GeraKuznetsov/M68K-MBC/Code/Boot/driver/SPI.c

#include "SPI.h"
#include "sys.h"

uint8_t const R1_READY_STATE = 0X00;
/** status for card in the idle state */
uint8_t const R1_IDLE_STATE = 0X01;
/** status bit for illegal command */
uint8_t const R1_ILLEGAL_COMMAND = 0X04;
/** start data token for read or write single block*/
uint8_t const DATA_START_BLOCK = 0XFE;
/** stop token for write multiple blocks*/
uint8_t const STOP_TRAN_TOKEN = 0XFD;
/** start data token for write multiple blocks*/
uint8_t const WRITE_MULTIPLE_TOKEN = 0XFC;
/** mask for data response tokens after a write block operation */
uint8_t const DATA_RES_MASK = 0X1F;
/** write data accepted token */
uint8_t const DATA_RES_ACCEPTED = 0X05;

/** Standard capacity V1 SD card */
uint8_t const SD_CARD_TYPE_SD1 = 1;
/** Standard capacity V2 SD card */
uint8_t const SD_CARD_TYPE_SD2 = 2;
/** High Capacity SD card */
uint8_t const SD_CARD_TYPE_SDHC = 3;

#define CS_LOW() SYS_PORT_RESET(SYS_OUT_PORT_SPI_CE0)
#define CS_HIGH() SYS_PORT_SET(SYS_OUT_PORT_SPI_CE0)

static volatile DSTATUS Stat = STA_NOINIT;	/* Disk status */
u8 CardType;

DSTATUS mmc_disk_status (void)
{
	return Stat;
}

static int wait_ready (	/* 1:Ready, 0:Timeout */
	u16 wt			/* Timeout [ms] */
){
	u8 d;

	wt /= 10;
	for(u32 i = 0; d != 0xFF & i < 125000; i++){ //TODO: timer
		d = SPI_SEND(0xFF);
	}

	return (d == 0xFF) ? 1 : 0;
}

static void deselect(){
	CS_HIGH();		/* Set CS# high */
	SPI_SEND(0xFF);	/* Dummy clock (force DO hi-z for multiple slave SPI) */
}

static int select()	/* 1:Successful, 0:Timeout */
{
	CS_LOW();		/* Set CS# low */
	SPI_SEND(0xFF);	/* Dummy clock (force DO enabled) */

	if (wait_ready(500)) return 1;	/* Leading busy check: Wait for card ready */

	deselect();		/* Timeout */
	return 0;
}

u8 send_cmd (		/* Returns R1 resp (bit7==1:Send failed) */
	u8 cmd,		/* Command index */
	u32 arg		/* Argument */
)
{
	u8 n, res;


	if (cmd & 0x80) {	/* ACMD<n> is the command sequense of CMD55-CMD<n> */
		cmd &= 0x7F;
		res = send_cmd(CMD55, 0);
		if (res > 1) return res;
	}

	/* Select the card and wait for ready except to stop multiple block read */
	if (cmd != CMD12) {
		deselect();
		if (!select()) return 0xFF;
	}

	/* Send command packet */
	SPI_SEND(0x40 | cmd);				/* Start + Command index */
	SPI_SEND((u8)(arg >> 24));		/* Argument[31..24] */
	SPI_SEND((u8)(arg >> 16));		/* Argument[23..16] */
	SPI_SEND((u8)(arg >> 8));			/* Argument[15..8] */
	SPI_SEND((u8)arg);				/* Argument[7..0] */
	n = 0x01;							/* Dummy CRC + Stop */
	if (cmd == CMD0) n = 0x95;			/* Valid CRC for CMD0(0) + Stop */
	if (cmd == CMD8) n = 0x87;			/* Valid CRC for CMD8(0x1AA) Stop */
	SPI_SEND(n);

	/* Receive command response */
	if (cmd == CMD12) SPI_SEND(0xFF);		/* Skip a stuff u8 when stop reading */
	n = 10;								/* Wait for a valid response in timeout of 10 attempts */
	do
		res = SPI_SEND(0xFF);
	while ((res & 0x80) && --n);

	return res;			/* Return with the response value */
}

void panic(unsigned char* message);

DSTATUS mmc_disk_initialize (void)
{
	BYTE n, cmd, ty, ocr[4];
	Stat = STA_NOINIT;

	//power_off();						/* Turn off the socket power to reset the card */
	for(u32 i = 0; i < 125000; i++){	/* Wait for 100ms */
		__asm__("nop ");
	}	

	//if (Stat & STA_NODISK) return Stat;	/* No card in the socket? */

	//power_on();							/* Turn on the socket power */
	SPI_SET_SPEED(SPI_SLOW);
	for (n = 10; n; n--) SPI_SEND(0xFF);	/* 80 dummy clocks */

	ty = 0;
	if (send_cmd(CMD0, 0) == 1) {			/* Put the card SPI mode */
		u16 attempt = 1000;						/* Initialization timeout of 1000 msec */
		if (send_cmd(CMD8, 0x1AA) == 1) {	/* Is the card SDv2? */
			for (n = 0; n < 4; n++) ocr[n] = SPI_SEND(0xFF);	/* Get trailing return value of R7 resp */
			if (ocr[2] == 0x01 && ocr[3] == 0xAA) {				/* The card can work at vdd range of 2.7-3.6V */
				while (attempt && send_cmd(ACMD41, 1UL << 30)){ attempt--;	}/* Wait for leaving idle state (ACMD41 with HCS bit) */
				if (attempt && send_cmd(CMD58, 0) == 0) {		/* Check CCS bit in the OCR */
					for (n = 0; n < 4; n++) ocr[n] = SPI_SEND(0xFF);
					ty = (ocr[0] & 0x40) ? CT_SDC2 | CT_BLOCK : CT_SDC2;	/* Check if the card is SDv2 */
				}
			}
		} else {							/* SDv1 or MMCv3 */
			if (send_cmd(ACMD41, 0) <= 1) 	{
				ty = CT_SDC1; cmd = ACMD41;	/* SDv1 */
			} else {
				ty = CT_MMC3; cmd = CMD1;	/* MMCv3 */
			}
			while (attempt && send_cmd(cmd, 0)){attempt--;};			/* Wait for leaving idle state */
			if (!attempt || send_cmd(CMD16, 512) != 0)	/* Set R/W block length to 512 */
				ty = 0;
		}
	}
	CardType = ty;
	deselect();

	if (ty) {			/* Initialization succeded */
		Stat &= ~STA_NOINIT;		/* Clear STA_NOINIT */
		SPI_SET_SPEED(SPI_FAST);
	} else {			/* Initialization failed */
		//power_off();
	}
	
	//return ty;
	return Stat;
}


void rcvr_spi_multi (
	BYTE *buff,	/* Pointer to read buffer */
	UINT bc		/* Number of bytes to receive */
){
	do {
		*buff = SPI_SEND(0xFF);			/* Store a received byte */
		buff++;
	} while (--bc);
}

static int rcvr_datablock (
	BYTE *buff,			/* Data buffer to store received data */
	UINT btr			/* Byte count (must be multiple of 4) */
){
	BYTE token;

	//Timer1 = 20;
	u32 attempt = 200000;
	do {							/* Wait for data packet in timeout of 200ms */
		token = SPI_SEND(0xFF);
		attempt--;
	} while ((token == 0xFF) && attempt);
	//} while ((token == 0xFF) && Timer1);
	if (token != 0xFE) return 0;	/* If not valid data token, retutn with error */

	rcvr_spi_multi(buff, btr);		/* Receive the data block into buffer */
	SPI_SEND(0xFF);					/* Discard CRC */
	SPI_SEND(0xFF);

	return 1;						/* Return with success */
}

/*-----------------------------------------------------------------------*/
/* Read Sector(s)                                                        */
/*-----------------------------------------------------------------------*/

DRESULT mmc_disk_read (
	BYTE *buff,			/* Pointer to the data buffer to store read data */
	LBA_t sector,		/* Start sector number (LBA) */
	UINT count			/* Sector count (1..128) */
)
{
	BYTE cmd;
	DWORD sect = (DWORD)sector;

	if (!count) return RES_PARERR;
	if (Stat & STA_NOINIT) return RES_NOTRDY;

	if (!(CardType & CT_BLOCK)) sect *= 512;	/* Convert to byte address if needed */

	cmd = count > 1 ? CMD18 : CMD17;			/*  READ_MULTIPLE_BLOCK : READ_SINGLE_BLOCK */
	if (send_cmd(cmd, sect) == 0) {
		do {
			if (!rcvr_datablock(buff, 512)) break;
			buff += 512;
		} while (--count);
		if (cmd == CMD18) send_cmd(CMD12, 0);	/* STOP_TRANSMISSION */
	}
	deselect();

	return count ? RES_ERROR : RES_OK;
}

/*-----------------------------------------------------------------------*/
/* Miscellaneous Functions                                               */
/*-----------------------------------------------------------------------*/

static void xmit_spi_multi (
	const BYTE *p,	/* Data block to be sent */
	UINT cnt		/* Size of data block */
)
{
	do {
		SPI_SEND(*p++);
	} while (--cnt);
}

static int xmit_datablock (
	const BYTE *buff,	/* 512 byte data block to be transmitted */
	BYTE token			/* Data/Stop token */
)
{
	BYTE resp;

	if (!wait_ready(500)) return 0;		/* Leading busy check: Wait for card ready to accept data block */

	SPI_SEND(token);					/* Xmit data token */
	if (token == 0xFD) return 1;		/* Do not send data if token is StopTran */

	xmit_spi_multi(buff, 512);			/* Data */
	SPI_SEND(0xFF); SPI_SEND(0xFF);		/* Dummy CRC */

	resp = SPI_SEND(0xFF);				/* Receive data resp */

	return (resp & 0x1F) == 0x05 ? 1 : 0;	/* Data was accepted or not */

	/* Busy check is done at next transmission */
}

DRESULT mmc_disk_ioctl (
	BYTE cmd,		/* Control code */
	void *buff		/* Buffer to send/receive control data */
)
{
	DRESULT res;
	BYTE n, csd[16], *ptr = buff;
	DWORD csize;
#if FF_USE_TRIM
	LBA_t *range;
	DWORD st, ed;
#endif
#if _USE_ISDIO
	SDIO_CTRL *sdi;
	BYTE rc, *bp;
	UINT dc;
#endif

	if (Stat & STA_NOINIT) return RES_NOTRDY;

	res = RES_ERROR;
	switch (cmd) {
	case CTRL_SYNC :		/* Make sure that no pending write process. Do not remove this or written sector might not left updated. */
		if (select()) res = RES_OK;
		deselect();
		break;

	case GET_SECTOR_COUNT :	/* Get number of sectors on the disk (DWORD) */
		if ((send_cmd(CMD9, 0) == 0) && rcvr_datablock(csd, 16)) {
			if ((csd[0] >> 6) == 1) {	/* SDC ver 2.00 */
				csize = csd[9] + ((WORD)csd[8] << 8) + ((DWORD)(csd[7] & 63) << 16) + 1;
				*(LBA_t*)buff = csize << 10;
			} else {					/* SDC ver 1.XX or MMC*/
				n = (csd[5] & 15) + ((csd[10] & 128) >> 7) + ((csd[9] & 3) << 1) + 2;
				csize = (csd[8] >> 6) + ((WORD)csd[7] << 2) + ((WORD)(csd[6] & 3) << 10) + 1;
				*(LBA_t*)buff = csize << (n - 9);
			}
			res = RES_OK;
		}
		deselect();
		break;

	case GET_BLOCK_SIZE :	/* Get erase block size in unit of sector (DWORD) */
		if (CardType & CT_SDC2) {	/* SDv2? */
			if (send_cmd(ACMD13, 0) == 0) {	/* Read SD status */
				SPI_SEND(0xFF);
				if (rcvr_datablock(csd, 16)) {				/* Read partial block */
					for (n = 64 - 16; n; n--) SPI_SEND(0xFF);	/* Purge trailing data */
					*(DWORD*)buff = 16UL << (csd[10] >> 4);
					res = RES_OK;
				}
			}
		} else {					/* SDv1 or MMCv3 */
			if ((send_cmd(CMD9, 0) == 0) && rcvr_datablock(csd, 16)) {	/* Read CSD */
				if (CardType & CT_SDC1) {	/* SDv1 */
					*(DWORD*)buff = (((csd[10] & 63) << 1) + ((WORD)(csd[11] & 128) >> 7) + 1) << ((csd[13] >> 6) - 1);
				} else {					/* MMCv3 */
					*(DWORD*)buff = ((WORD)((csd[10] & 124) >> 2) + 1) * (((csd[11] & 3) << 3) + ((csd[11] & 224) >> 5) + 1);
				}
				res = RES_OK;
			}
		}
		deselect();
		break;
#if FF_USE_TRIM
	case CTRL_TRIM:		/* Erase a block of sectors (used when _USE_TRIM in ffconf.h is 1) */
		if (!(CardType & CT_SDC)) break;				/* Check if the card is SDC */
		if (mmc_disk_ioctl(MMC_GET_CSD, csd)) break;	/* Get CSD */
		if (!(csd[10] & 0x40)) break;					/* Check if ERASE_BLK_EN = 1 */
		range = buff; st = (DWORD)range[0]; ed = (DWORD)range[1];	/* Load sector block */
		if (!(CardType & CT_BLOCK)) {
			st *= 512; ed *= 512;
		}
		if (send_cmd(CMD32, st) == 0 && send_cmd(CMD33, ed) == 0 && send_cmd(CMD38, 0) == 0 && wait_ready(60000)) {	/* Erase sector block */
			res = RES_OK;	/* FatFs does not check result of this command */
		}
		break;
#endif
	/* Following commands are never used by FatFs module */

	case MMC_GET_TYPE :		/* Get card type flags (1 byte) */
		*ptr = CardType;
		res = RES_OK;
		break;

	case MMC_GET_CSD :		/* Receive CSD as a data block (16 bytes) */
		if (send_cmd(CMD9, 0) == 0 && rcvr_datablock(ptr, 16)) {	/* READ_CSD */
			res = RES_OK;
		}
		deselect();
		break;

	case MMC_GET_CID :		/* Receive CID as a data block (16 bytes) */
		if (send_cmd(CMD10, 0) == 0 && rcvr_datablock(ptr, 16)) {	/* READ_CID */
			res = RES_OK;
		}
		deselect();
		break;

	case MMC_GET_OCR :		/* Receive OCR as an R3 resp (4 bytes) */
		if (send_cmd(CMD58, 0) == 0) {	/* READ_OCR */
			for (n = 4; n; n--) *ptr++ = SPI_SEND(0xFF);
			res = RES_OK;
		}
		deselect();
		break;

	case MMC_GET_SDSTAT :	/* Receive SD statsu as a data block (64 bytes) */
		if (send_cmd(ACMD13, 0) == 0) {	/* SD_STATUS */
			SPI_SEND(0xFF);
			if (rcvr_datablock(ptr, 64)) res = RES_OK;
		}
		deselect();
		break;

	/*case CTRL_POWER_OFF :	/* Power off 
		power_off();
		Stat |= STA_NOINIT;
		res = RES_OK;
		break;*/
#if _USE_ISDIO
	case ISDIO_READ:
		sdi = buff;
		if (send_cmd(CMD48, 0x80000000 | (DWORD)sdi->func << 28 | (DWORD)sdi->addr << 9 | ((sdi->ndata - 1) & 0x1FF)) == 0) {
			for (Timer1 = 100; (rc = SPI_SEND(0xFF)) == 0xFF && Timer1; ) ;
			if (rc == 0xFE) {
				for (bp = sdi->data, dc = sdi->ndata; dc; dc--) *bp++ = SPI_SEND(0xFF);
				for (dc = 514 - sdi->ndata; dc; dc--) SPI_SEND(0xFF);
				res = RES_OK;
			}
		}
		deselect();
		break;

	case ISDIO_WRITE:
		sdi = buff;
		if (send_cmd(CMD49, 0x80000000 | (DWORD)sdi->func << 28 | (DWORD)sdi->addr << 9 | ((sdi->ndata - 1) & 0x1FF)) == 0) {
			SPI_SEND(0xFF); SPI_SEND(0xFE);
			for (bp = sdi->data, dc = sdi->ndata; dc; dc--) SPI_SEND(*bp++);
			for (dc = 514 - sdi->ndata; dc; dc--) SPI_SEND(0xFF);
			if ((SPI_SEND(0xFF) & 0x1F) == 0x05) res = RES_OK;
		}
		deselect();
		break;

	case ISDIO_MRITE:
		sdi = buff;
		if (send_cmd(CMD49, 0x84000000 | (DWORD)sdi->func << 28 | (DWORD)sdi->addr << 9 | sdi->ndata >> 8) == 0) {
			SPI_SEND(0xFF); SPI_SEND(0xFE);
			SPI_SEND(sdi->ndata);
			for (dc = 513; dc; dc--) SPI_SEND(0xFF);
			if ((SPI_SEND(0xFF) & 0x1F) == 0x05) res = RES_OK;
		}
		deselect();
		break;
#endif
	default:
		res = RES_PARERR;
	}

	return res;
}

DRESULT mmc_disk_write (
	const BYTE *buff,	/* Pointer to the data to be written */
	LBA_t sector,		/* Start sector number (LBA) */
	UINT count			/* Sector count (1..128) */
)
{
	DWORD sect = (DWORD)sector;


	if (!count) return RES_PARERR;
	if (Stat & STA_NOINIT) return RES_NOTRDY;
	//if (Stat & STA_PROTECT) return RES_WRPRT;

	if (!(CardType & CT_BLOCK)) sect *= 512;	/* Convert to byte address if needed */

	if (count == 1) {	/* Single block write */
		if ((send_cmd(CMD24, sect) == 0)	/* WRITE_BLOCK */
			&& xmit_datablock(buff, 0xFE)) {
			count = 0;
		}
	}
	else {				/* Multiple block write */
		if (CardType & CT_SDC) send_cmd(ACMD23, count);
		if (send_cmd(CMD25, sect) == 0) {	/* WRITE_MULTIPLE_BLOCK */
			do {
				if (!xmit_datablock(buff, 0xFC)) break;
				buff += 512;
			} while (--count);
			if (!xmit_datablock(0, 0xFD)) count = 1;	/* STOP_TRAN token */
		}
	}
	deselect();

	return count ? RES_ERROR : RES_OK;
}
